greeniot/Arduino-Sample/source/cc3200/distance/Ultrasonic.cpp

#include "Ultrasonic.h"

Ultrasonic::Ultrasonic(int TP, int EP) {
   pinMode(TP, OUTPUT);
   pinMode(EP, INPUT);
   Trig_pin = TP;
   Echo_pin = EP;
   Time_out = 3000;  // 3000 µs = 50cm // 30000 µs = 5 m 
}

Ultrasonic::Ultrasonic(int TP, int EP, long TO) {
   pinMode(TP, OUTPUT);
   pinMode(EP, INPUT);
   Trig_pin = TP;
   Echo_pin = EP;
   Time_out = TO;
}

long Ultrasonic::Timing() {
  digitalWrite(Trig_pin, LOW);
  delayMicroseconds(2);
  digitalWrite(Trig_pin, HIGH);
  delayMicroseconds(10);
  digitalWrite(Trig_pin, LOW);
  duration = pulseIn(Echo_pin, HIGH, Time_out);

  if (duration == 0) {
	  duration = Time_out;
	}

  return duration;
}

float Ultrasonic::Ranging(int sys) {
  Timing();

  if (sys) {
	  distance_cm = duration / 29.0 * 0.5;
	  return distance_cm;
  } else {
	  distance_inch = duration / 74.0 * 0.5;
	  return distance_inch;
	}
}
